kszdomagh/NORAD-A/rtl/ROM/img_rom.sv

//////////////////////////////////////////////////////////////////////////////
/*
 Module name:   start_screen_rom
 Author:        IG, kszdom
 Description:   ROM memory for all used graphics and more

                after each object there is a RESET signal (LINE=1, POS=1)
 */
//////////////////////////////////////////////////////////////////////////////
module img_rom #(
    parameter int ADDRESSWIDTH = 4,  // 4 bits => 16 entries
    parameter int DATAWIDTH = 18  // 8+8+1+1 = 18 bits
)(
    input logic [ADDRESSWIDTH-1:0] addr,
    output logic [DATAWIDTH-1:0] data_out
);

    always_comb begin
        unique case (addr)
            //                  x       y       line    pos
            0:  data_out = {8'd0, 8'd0, 1'b0, 1'b1};



            //      USA MAP     TEMP
            1:  data_out = {8'd142, 8'd227, 1'b0, 1'b1};
            2:  data_out = {8'd131, 8'd225, 1'b1, 1'b0};
            3:  data_out = {8'd132, 8'd245, 1'b1, 1'b0};
            4:  data_out = {8'd111, 8'd209, 1'b1, 1'b0};
            5:  data_out = {8'd120, 8'd197, 1'b1, 1'b0};
            6:  data_out = {8'd101, 8'd187, 1'b1, 1'b0};
            7:  data_out = {8'd104, 8'd175, 1'b1, 1'b0};
            8:  data_out = {8'd108, 8'd132, 1'b1, 1'b0};
            9:  data_out = {8'd82, 8'd87, 1'b1, 1'b0};
            10:  data_out = {8'd100, 8'd60, 1'b1, 1'b0};
            11:  data_out = {8'd97, 8'd39, 1'b1, 1'b0};
            12:  data_out = {8'd75, 8'd68, 1'b1, 1'b0};
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
            629: data_out = {8'd15, 8'd2, 1'b1, 1'b0};
            630: data_out = {8'd22, 8'd2, 1'b1, 1'b0};
            631: data_out = {8'd22, 8'd2, 1'b1, 1'b1};  //  RESET





            

            default: data_out = {8'd0, 8'd0, 1'b1, 1'b1};
        endcase
    end

endmodule
