kszdomagh/NORAD-A/rtl/ROM/end_screen_rom.sv

//////////////////////////////////////////////////////////////////////////////
/*
 Module name:   ending_screen_rom
 Author:        kszdom
 Description:   ROM memory for ending screen


  _   _ _    _  _____ _      ______          _____                        
 | \ | | |  | |/ ____| |    |  ____|   /\   |  __ \                       
 |  \| | |  | | |    | |    | |__     /  \  | |__) |                      
 | . ` | |  | | |    | |    |  __|   / /\ \ |  _  /                       
 | |\  | |__| | |____| |____| |____ / ____ \| | \ \                       
 |_| \_|\____/_\_____|______|______/_/_ __\_\_|__\_\  _____   ____  _   _ 
     /\   |  __ \|  \/  |   /\   / ____|  ____|  __ \|  __ \ / __ \| \ | |
    /  \  | |__) | \  / |  /  \ | |  __| |__  | |  | | |  | | |  | |  \| |
   / /\ \ |  _  /| |\/| | / /\ \| | |_ |  __| | |  | | |  | | |  | | . ` |
  / ____ \| | \ \| |  | |/ ____ \ |__| | |____| |__| | |__| | |__| | |\  |
 /_/___ \_\_|_ \_\_| _|_/_/__  \_\_____|______|_____/|_____/ \____/|_| \_|
 |_   _|/ ____| | \ | |  ____|   /\   |  __ \                             
   | | | (___   |  \| | |__     /  \  | |__) |                            
   | |  \___ \  | . ` |  __|   / /\ \ |  _  /                             
  _| |_ ____) | | |\  | |____ / ____ \| | \ \                             
 |_____|_____/  |_| \_|______/_/    \_\_|  \_\ 

 */
//////////////////////////////////////////////////////////////////////////////



module end_screen_rom #(
    parameter int ADDRESSWIDTH = 4,  // 4 bits => 16 entries
    parameter int DATAWIDTH = 18  // 8+8+1+1 = 18 bits
)(
    input logic [ADDRESSWIDTH-1:0] addr,
    output logic [DATAWIDTH-1:0] data_out
);

    always_comb begin
        unique case (addr)
            //                  x       y       line    pos

            0: data_out = {8'd54, 8'd187, 1'b0, 1'b1};
            1: data_out = {8'd69, 8'd187, 1'b1, 1'b0};
            2: data_out = {8'd69, 8'd194, 1'b1, 1'b0};
            3: data_out = {8'd54, 8'd194, 1'b1, 1'b0};
            4: data_out = {8'd54, 8'd187, 1'b1, 1'b0};
            5: data_out = {8'd46, 8'd163, 1'b0, 1'b1};
            6: data_out = {8'd53, 8'd163, 1'b1, 1'b0};
            7: data_out = {8'd53, 8'd186, 1'b1, 1'b0};
            8: data_out = {8'd46, 8'd186, 1'b1, 1'b0};
            9: data_out = {8'd46, 8'd163, 1'b1, 1'b0};
            10: data_out = {8'd54, 8'd155, 1'b0, 1'b1};
            11: data_out = {8'd69, 8'd155, 1'b1, 1'b0};
            12: data_out = {8'd69, 8'd162, 1'b1, 1'b0};
            13: data_out = {8'd54, 8'd162, 1'b1, 1'b0};
            14: data_out = {8'd54, 8'd155, 1'b1, 1'b0};
            15: data_out = {8'd62, 8'd171, 1'b0, 1'b1};
            16: data_out = {8'd77, 8'd171, 1'b1, 1'b0};
            17: data_out = {8'd77, 8'd178, 1'b1, 1'b0};
            18: data_out = {8'd62, 8'd178, 1'b1, 1'b0};
            19: data_out = {8'd62, 8'd171, 1'b1, 1'b0};
            20: data_out = {8'd70, 8'd171, 1'b0, 1'b1};
            21: data_out = {8'd70, 8'd163, 1'b1, 1'b0};
            22: data_out = {8'd77, 8'd163, 1'b1, 1'b0};
            23: data_out = {8'd77, 8'd171, 1'b1, 1'b0};
            24: data_out = {8'd86, 8'd155, 1'b0, 1'b1};
            25: data_out = {8'd93, 8'd155, 1'b1, 1'b0};
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
            153: data_out = {8'd199, 8'd106, 1'b1, 1'b0};
            154: data_out = {8'd199, 8'd99, 1'b1, 1'b0};
            155: data_out = {8'd199, 8'd75, 1'b0, 1'b1};
            156: data_out = {8'd206, 8'd75, 1'b1, 1'b0};
            157: data_out = {8'd206, 8'd82, 1'b1, 1'b0};
            158: data_out = {8'd199, 8'd82, 1'b1, 1'b0};
            159: data_out = {8'd199, 8'd75, 1'b1, 1'b0};
            160: data_out = {8'd182, 8'd107, 1'b0, 1'b1};
            161: data_out = {8'd198, 8'd107, 1'b1, 1'b0};
            162: data_out = {8'd198, 8'd114, 1'b1, 1'b0};
            163: data_out = {8'd182, 8'd114, 1'b1, 1'b0};
            164: data_out = {8'd182, 8'd91, 1'b0, 1'b1};
            165: data_out = {8'd198, 8'd91, 1'b1, 1'b0};
            166: data_out = {8'd198, 8'd98, 1'b1, 1'b0};
            167: data_out = {8'd182, 8'd98, 1'b1, 1'b0};
            168: data_out = {8'd191, 8'd91, 1'b0, 1'b1};
            169: data_out = {8'd191, 8'd83, 1'b1, 1'b0};
            170: data_out = {8'd198, 8'd83, 1'b1, 1'b0};
            171: data_out = {8'd198, 8'd91, 1'b1, 1'b0};
            172: data_out = {8'd198, 8'd91, 1'b1, 1'b1};    // RESET



            default: data_out = '0;
        endcase
    end

endmodule
