kszdomagh/NORAD-A/rtl/ROM/start_screen_rom.sv

//////////////////////////////////////////////////////////////////////////////
/*
 Module name:   start_screen_rom
 Author:        kszdom, IG
 Description:   ROM memory for starting screen


  _   _ _    _  _____ _      ______          _____                        
 | \ | | |  | |/ ____| |    |  ____|   /\   |  __ \                       
 |  \| | |  | | |    | |    | |__     /  \  | |__) |                      
 | . ` | |  | | |    | |    |  __|   / /\ \ |  _  /                       
 | |\  | |__| | |____| |____| |____ / ____ \| | \ \                       
 |_| \_|\____/_\_____|______|______/_/_ __\_\_|__\_\  _____   ____  _   _ 
     /\   |  __ \|  \/  |   /\   / ____|  ____|  __ \|  __ \ / __ \| \ | |
    /  \  | |__) | \  / |  /  \ | |  __| |__  | |  | | |  | | |  | |  \| |
   / /\ \ |  _  /| |\/| | / /\ \| | |_ |  __| | |  | | |  | | |  | | . ` |
  / ____ \| | \ \| |  | |/ ____ \ |__| | |____| |__| | |__| | |__| | |\  |
 /_/___ \_\_|_ \_\_| _|_/_/__  \_\_____|______|_____/|_____/ \____/|_| \_|
 |_   _|/ ____| | \ | |  ____|   /\   |  __ \                             
   | | | (___   |  \| | |__     /  \  | |__) |                            
   | |  \___ \  | . ` |  __|   / /\ \ |  _  /                             
  _| |_ ____) | | |\  | |____ / ____ \| | \ \                             
 |_____|_____/  |_| \_|______/_/    \_\_|  \_\ 

 */
//////////////////////////////////////////////////////////////////////////////



module start_screen_rom #(
    parameter int ADDRESSWIDTH = 14,  // 4 bits => 16 entries
    parameter int DATAWIDTH = 18  // 8+8+1+1 = 18 bits
)(
    input logic [ADDRESSWIDTH-1:0] addr,
    output logic [DATAWIDTH-1:0] data_out
);


    always_comb begin
        unique case (addr)

            0: data_out = {8'd13, 8'd51, 1'b0, 1'b1};
            1: data_out = {8'd21, 8'd51, 1'b1, 1'b0};
            2: data_out = {8'd21, 8'd53, 1'b1, 1'b0};
            3: data_out = {8'd13, 8'd53, 1'b1, 1'b0};
            4: data_out = {8'd13, 8'd51, 1'b1, 1'b0};
            5: data_out = {8'd22, 8'd54, 1'b0, 1'b1};
            6: data_out = {8'd24, 8'd54, 1'b1, 1'b0};
            7: data_out = {8'd24, 8'd56, 1'b1, 1'b0};
            8: data_out = {8'd22, 8'd56, 1'b1, 1'b0};
            9: data_out = {8'd22, 8'd54, 1'b1, 1'b0};
            10: data_out = {8'd21, 8'd57, 1'b0, 1'b1};
            11: data_out = {8'd21, 8'd59, 1'b1, 1'b0};
            12: data_out = {8'd16, 8'd59, 1'b1, 1'b0};
            13: data_out = {8'd16, 8'd57, 1'b1, 1'b0};
            14: data_out = {8'd21, 8'd57, 1'b1, 1'b0};
            15: data_out = {8'd15, 8'd60, 1'b0, 1'b1};
            16: data_out = {8'd15, 8'd62, 1'b1, 1'b0};
            17: data_out = {8'd13, 8'd62, 1'b1, 1'b0};
            18: data_out = {8'd13, 8'd60, 1'b1, 1'b0};
            19: data_out = {8'd15, 8'd60, 1'b1, 1'b0};
            20: data_out = {8'd16, 8'd63, 1'b0, 1'b1};
            21: data_out = {8'd24, 8'd63, 1'b1, 1'b0};
            22: data_out = {8'd24, 8'd65, 1'b1, 1'b0};
            23: data_out = {8'd16, 8'd65, 1'b1, 1'b0};
            24: data_out = {8'd16, 8'd63, 1'b1, 1'b0};
            25: data_out = {8'd28, 8'd51, 1'b0, 1'b1};
            26: data_out = {8'd30, 8'd51, 1'b1, 1'b0};
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
            389: data_out = {8'd221, 8'd216, 1'b0, 1'b1};
            390: data_out = {8'd236, 8'd216, 1'b1, 1'b0};
            391: data_out = {8'd236, 8'd216, 1'b1, 1'b1};

            default: data_out = {8'd0, 8'd0, 1'b1, 1'b1};
        endcase
    end

endmodule
