kszdomagh/NORAD-A/rtl/mmcm/clk_wiz_0_clk_wiz.v

// file: clk_wiz_0.v
// (c) Copyright 2017-2018, 2023 Advanced Micro Devices, Inc. All rights reserved.
//
// This file contains confidential and proprietary information
// of AMD and is protected under U.S. and international copyright
// and other intellectual property laws.
//
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
// CRITICAL APPLICATIONS
// AMD products are not designed or intended to be fail-
// safe, or for use in any application requiring fail-safe
// performance, such as life-support or safety devices or
// systems, Class III medical devices, nuclear facilities,
// applications related to the deployment of airbags, or any
// other applications that could lead to death, personal
// injury, or severe property or environmental damage
// (individually and collectively, "Critical
// Applications"). Customer assumes the sole risk and
// liability of any use of AMD products in Critical
// Applications, subject only to applicable laws and
// regulations governing limitations on product liability.
//
// THIS COPYRIGHT NOTICE AND DISCLAIMER MUST BE RETAINED AS
// PART OF THIS FILE AT ALL TIMES.
//----------------------------------------------------------------------------
// User entered comments
//----------------------------------------------------------------------------
// None
//
//----------------------------------------------------------------------------
//  Output     Output      Phase    Duty Cycle   Pk-to-Pk     Phase
//   Clock     Freq (MHz)  (degrees)    (%)     Jitter (ps)  Error (ps)
//----------------------------------------------------------------------------
// clk100MHz__100.00000______0.000______50.0______146.945____126.282
// clk80MHz__79.68750______0.000______50.0______154.114____126.282
// _clk5MHz___4.98047______0.000______50.0______267.870____126.282
//
//----------------------------------------------------------------------------
// Input Clock   Freq (MHz)    Input Jitter (UI)
//----------------------------------------------------------------------------
// __primary_________100.000____________0.010

`timescale 1ps/1ps

module clk_wiz_0_clk_wiz 

 (// Clock in ports
  // Clock out ports
  output        clk100MHz,
  output        clk80MHz,
  output        clk5MHz,
  // Status and control signals
  input         reset,
  input         clk_in1
 );
  // Input buffering
  //------------------------------------
wire clk_in1_clk_wiz_0;
wire clk_in2_clk_wiz_0;
  IBUF clkin1_ibufg
   (.O (clk_in1_clk_wiz_0),
    .I (clk_in1));




  // Clocking PRIMITIVE
  //------------------------------------

  // Instantiation of the MMCM PRIMITIVE
  //    * Unused inputs are tied off
  //    * Unused outputs are labeled unused

  wire        clk100MHz_clk_wiz_0;
  wire        clk80MHz_clk_wiz_0;
  wire        clk5MHz_clk_wiz_0;
  wire        clk_out4_clk_wiz_0;
  wire        clk_out5_clk_wiz_0;
  wire        clk_out6_clk_wiz_0;
  wire        clk_out7_clk_wiz_0;

  wire [15:0] do_unused;
  wire        drdy_unused;
  wire        psdone_unused;
  wire        locked_int;
  wire        clkfbout_clk_wiz_0;
  wire        clkfbout_buf_clk_wiz_0;
  wire        clkfboutb_unused;
    wire clkout0b_unused;
   wire clkout1b_unused;
   wire clkout2b_unused;
   wire clkout3_unused;
   wire clkout3b_unused;
   wire clkout4_unused;
  wire        clkout5_unused;
  wire        clkout6_unused;
  wire        clkfbstopped_unused;
  wire        clkinstopped_unused;
  wire        reset_high;

  MMCME2_ADV
  #(.BANDWIDTH            ("OPTIMIZED"),
    .CLKOUT4_CASCADE      ("FALSE"),
    .COMPENSATION         ("ZHOLD"),
    .STARTUP_WAIT         ("FALSE"),
    .DIVCLK_DIVIDE        (1),
    .CLKFBOUT_MULT_F      (6.375),
    .CLKFBOUT_PHASE       (0.000),
    .CLKFBOUT_USE_FINE_PS ("FALSE"),
    .CLKOUT0_DIVIDE_F     (6.375),
    .CLKOUT0_PHASE        (0.000),
    .CLKOUT0_DUTY_CYCLE   (0.500),
    .CLKOUT0_USE_FINE_PS  ("FALSE"),
    .CLKOUT1_DIVIDE       (8),
    .CLKOUT1_PHASE        (0.000),
    .CLKOUT1_DUTY_CYCLE   (0.500),
    .CLKOUT1_USE_FINE_PS  ("FALSE"),
    .CLKOUT2_DIVIDE       (128),
    .CLKOUT2_PHASE        (0.000),
    .CLKOUT2_DUTY_CYCLE   (0.500),
    .CLKOUT2_USE_FINE_PS  ("FALSE"),
    .CLKIN1_PERIOD        (10.000))
  mmcm_adv_inst
    // Output clocks
   (
    .CLKFBOUT            (clkfbout_clk_wiz_0),
    .CLKFBOUTB           (clkfboutb_unused),
    .CLKOUT0             (clk100MHz_clk_wiz_0),
    .CLKOUT0B            (clkout0b_unused),
    .CLKOUT1             (clk80MHz_clk_wiz_0),
    .CLKOUT1B            (clkout1b_unused),
    .CLKOUT2             (clk5MHz_clk_wiz_0),
    .CLKOUT2B            (clkout2b_unused),
    .CLKOUT3             (clkout3_unused),
    .CLKOUT3B            (clkout3b_unused),
    .CLKOUT4             (clkout4_unused),
    .CLKOUT5             (clkout5_unused),
    .CLKOUT6             (clkout6_unused),
     // Input clock control
    .CLKFBIN             (clkfbout_buf_clk_wiz_0),
    .CLKIN1              (clk_in1_clk_wiz_0),
    .CLKIN2              (1'b0),
     // Tied to always select the primary input clock
    .CLKINSEL            (1'b1),
    // Ports for dynamic reconfiguration
    .DADDR               (7'h0),
    .DCLK                (1'b0),
    .DEN                 (1'b0),
    .DI                  (16'h0),
    .DO                  (do_unused),
    .DRDY                (drdy_unused),
    .DWE                 (1'b0),
    // Ports for dynamic phase shift
    .PSCLK               (1'b0),
    .PSEN                (1'b0),
    .PSINCDEC            (1'b0),
    .PSDONE              (psdone_unused),
    // Other control and status signals
    .LOCKED              (locked_int),
    .CLKINSTOPPED        (clkinstopped_unused),
    .CLKFBSTOPPED        (clkfbstopped_unused),
    .PWRDWN              (1'b0),
    .RST                 (reset_high));
  assign reset_high = reset; 

// Clock Monitor clock assigning
//--------------------------------------
 // Output buffering
  //-----------------------------------

  BUFG clkf_buf
   (.O (clkfbout_buf_clk_wiz_0),
    .I (clkfbout_clk_wiz_0));






  BUFG clkout1_buf
   (.O   (clk100MHz),
    .I   (clk100MHz_clk_wiz_0));


  BUFG clkout2_buf
   (.O   (clk80MHz),
    .I   (clk80MHz_clk_wiz_0));

  BUFG clkout3_buf
   (.O   (clk5MHz),
    .I   (clk5MHz_clk_wiz_0));



endmodule
