kszdomagh/NORAD-A/rtl/ROM/mtm_rom.sv

//////////////////////////////////////////////////////////////////////////////
/*
 Module name:   mtm_rom
 Author:        kszdom
 Description:   ROM memory for MTM logo
 */
//////////////////////////////////////////////////////////////////////////////
module mtm_rom #(
    parameter int ADDRESSWIDTH = 14,  // 4 bits => 16 entries
    parameter int DATAWIDTH = 18  // 8+8+1+1 = 18 bits
)(
    input logic [ADDRESSWIDTH-1:0] addr,
    output logic [DATAWIDTH-1:0] data_out
);


    always_comb begin
        unique case (addr)
			//                  x       y       line    pos
            0:  data_out = {8'd32, 8'd98, 1'b0, 1'b1};
            1:  data_out = {8'd33, 8'd94, 1'b1, 1'b0};
            2:  data_out = {8'd35, 8'd92, 1'b1, 1'b0};
            3:  data_out = {8'd41, 8'd92, 1'b1, 1'b0};
            4:  data_out = {8'd44, 8'd95, 1'b1, 1'b0};
            5:  data_out = {8'd44, 8'd101, 1'b1, 1'b0};
            6:  data_out = {8'd41, 8'd104, 1'b1, 1'b0};
            7:  data_out = {8'd35, 8'd104, 1'b1, 1'b0};
            8:  data_out = {8'd32, 8'd98, 1'b1, 1'b0};
            9:  data_out = {8'd32, 8'd173, 1'b0, 1'b1};
            10:  data_out = {8'd37, 8'd175, 1'b1, 1'b0};
            11:  data_out = {8'd63, 8'd175, 1'b1, 1'b0};
            12:  data_out = {8'd66, 8'd172, 1'b1, 1'b0};
            13:  data_out = {8'd80, 8'd128, 1'b1, 1'b0};
            14:  data_out = {8'd83, 8'd125, 1'b1, 1'b0};
            15:  data_out = {8'd87, 8'd126, 1'b1, 1'b0};
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
            63:  data_out = {8'd217, 8'd95, 1'b1, 1'b0};
            64:  data_out = {8'd217, 8'd99, 1'b1, 1'b0};
            65:  data_out = {8'd217, 8'd99, 1'b1, 1'b1};        //  RESET



            default: data_out = {8'd0, 8'd0, 1'b1, 1'b1};
        endcase
    end

endmodule
