kszdomagh/NORAD-A/sim/top_rtl/top_rtl_tb.sv

//////////////////////////////////////////////////////////////////////////////
/*
 Module name:   top_rtl_tb
 Author:        kszdom
 Description:   testbench module for top_rtl
 */
//////////////////////////////////////////////////////////////////////////////

module top_rtl_tb;

    // Testbench signals
    logic clk100MHz;
    logic clk40MHz;
    logic clk4MHz;
    logic rst;

    import vector_pkg::*;
    import img_pkg::*;

    // INTERNAL WIRES
    logic halt_flag;
    logic go_flag;
    logic [OUT_WIDTH-1:0] xsignal;
    logic [OUT_WIDTH-1:0] ysignal;

    logic startgame;
    logic button_click;
    logic mtm_show;
    logic show_death;

    //MODULE DECLARATIONS
    top_rtl #(
        .ADDRESSWIDTH(ADDRESSWIDTH),
        .DATAWIDTH(DATAWIDTH),
        .OUT_WIDTH(OUT_WIDTH)
    ) u_DUT (
        .clk_fast(clk100MHz),
        .clk_slow(clk4MHz),
        .rst(rst),

        .go_flag(go_flag),
        .halt_flag(halt_flag),

        .startgame(startgame),
        .mtm_show(mtm_show),
        .show_death(show_death),


        .xcursor(8'd200),
        .ycursor(8'd60),
        .button_click(button_click),

        .xch(xsignal),
        .ych(ysignal)
    );
    // Clock generation
    initial begin
        clk100MHz = 0;
        forever #5 clk100MHz = ~clk100MHz; // 100MHz
    end

    initial begin
        clk40MHz = 0;
        forever #12.5 clk40MHz = ~clk40MHz; // 40MHz
    end

    initial begin
        clk4MHz = 0;
        forever #125 clk4MHz = ~clk4MHz; // 4MHz
    end

    // Stimulus block
    initial begin
        rst = 1;
        #20 rst = 0;

        show_death = 0;
        mtm_show = 0;
        startgame = 1;          //CHANGE THIS TO 1 TO SEE THE GAME
        button_click = 1;

        // Optional: add timeout
        #10000000000;
        $display("Simulation timeout reached.");
        $finish;
    end


    integer fd;
    initial begin
        fd = $fopen("../.output_files/top_rtl_results.txt", "w");
        if (fd == 0) $fatal("Cannot open file!");
        forever begin
            @(posedge clk4MHz);
            $fwrite(fd, "x=%d, y=%d\n",xsignal,ysignal);
        end
    end

    int halt_count = 0;

    always @(posedge clk100MHz) begin
        
        if (halt_count == 4) begin
            $display("Recieved HALT signal at time: %t", $time);
            $display("Ending simulation. Check output files.");
            $display("PASSED :3");
            $finish;
        end

    end

    always @(posedge halt_flag) begin
        $display("halt count inc");
        halt_count <= halt_count + 1;
    end



endmodule
